lfiack/witns_dsp_som/firmware/grnlr/Core/Inc/main.h

#define __sdram __attribute__((section(".sdram_data")))
#define LED_Pin GPIO_PIN_3
#define LED_GPIO_Port GPIOC
#define VCP_TX_Pin GPIO_PIN_0
#define VCP_TX_GPIO_Port GPIOA
#define VCP_RX_Pin GPIO_PIN_1
#define VCP_RX_GPIO_Port GPIOA
#define ENC_A_Pin GPIO_PIN_2
#define ENC_A_GPIO_Port GPIOA
#define ENC_A_EXTI_IRQn EXTI2_IRQn
#define ENC_B_Pin GPIO_PIN_3
#define ENC_B_GPIO_Port GPIOA
#define OLED_RESET_Pin GPIO_PIN_12
#define OLED_RESET_GPIO_Port GPIOD
#define ENC_PB_Pin GPIO_PIN_13
#define ENC_PB_GPIO_Port GPIOD
#define ENC_PB_EXTI_IRQn EXTI15_10_IRQn
#define SD_DETECT_Pin GPIO_PIN_7
#define SD_DETECT_GPIO_Port GPIOB
