lfiack/witns_dsp_som/firmware/sgtl5000/sgtl5000.h

/*
 * sgtl5000.h
 *
 *  Created on: Oct 14, 2025
 *      Author: laurentf
 */

#ifndef SGTL5000_SGTL5000_H_
#define SGTL5000_SGTL5000_H_

#include "main.h"

typedef enum sgtl5000_registers_enum
{
	SGTL5000_CHIP_ID = 0x0000,
	SGTL5000_CHIP_DIG_POWER = 0x0002,
	SGTL5000_CHIP_CLK_CTRL = 0x0004,
	SGTL5000_CHIP_I2S_CTRL = 0x0006,
	SGTL5000_CHIP_SSS_CTRL = 0x000A,
	SGTL5000_CHIP_ADCDAC_CTRL = 0x000E,
	SGTL5000_CHIP_DAC_VOL = 0x0010,
	SGTL5000_CHIP_PAD_STRENGTH = 0x0014,
	SGTL5000_CHIP_ANA_ADC_CTRL = 0x0020,
	SGTL5000_CHIP_ANA_HP_CTRL = 0x0022,
	SGTL5000_CHIP_ANA_CTRL = 0x0024,
	SGTL5000_CHIP_LINREG_CTRL = 0x0026,
	SGTL5000_CHIP_REF_CTRL = 0x0028,
	SGTL5000_CHIP_MIC_CTRL = 0x002A,
	SGTL5000_CHIP_LINE_OUT_CTRL = 0x002C,
	SGTL5000_CHIP_LINE_OUT_VOL = 0x002E,
	SGTL5000_CHIP_ANA_POWER = 0x0030,
	SGTL5000_CHIP_PLL_CTRL = 0x0032,
	SGTL5000_CHIP_CLK_TOP_CTRL = 0x0034,
	SGTL5000_SHIP_ANA_STATUS = 0x0036,
	SGTL5000_CHIP_ANA_TEST1 = 0x0038,
	SGTL5000_CHIP_ANA_TEST2 = 0x003A,
	SGTL5000_CHIP_SHORT_CTRL = 0x003C,
	SGTL5000_DAP_CONTROL = 0x0100,
	SGTL5000_DAP_PEQ = 0x0102,
	SGTL5000_DAP_BASS_ENHANCE = 0x0104,
	SGTL5000_DAP_BASS_ENHANCE_CTRL = 0x0106,
	SGTL5000_DAP_AUDIO_EQ = 0x0108,
	SGTL5000_DAP_SGTL_SURROUND = 0x010A,
	SGTL5000_DAP_FILTER_COEF_ACCESS = 0x010C,
	SGTL5000_DAP_COEF_WR_B0_MSB = 0x010E,
	SGTL5000_DAP_COEF_WR_B0_LSB = 0x0110,
	SGTL5000_DAP_AUDIO_EQ_BASS_BAND0 = 0x0116,
	SGTL5000_DAP_AUDIO_EQ_BAND1 = 0x0118,
	SGTL5000_DAP_AUDIO_EQ_BAND2 = 0x011A,
	SGTL5000_DAP_AUDIO_EQ_BAND3 = 0x011C,
	SGTL5000_DAP_AUDIO_EQ_TREBLE_BAND4 = 0x011E,
	SGTL5000_DAP_MAIN_CHAN = 0x0120,
	SGTL5000_DAP_MIX_CHAN = 0x0122,
	SGTL5000_DAP_AVC_CTRL = 0x0124,
	SGTL5000_DAP_AVC_THRESHOLD = 0x0126,
	SGTL5000_DAP_AVC_ATTACK = 0x0128,
	SGTL5000_DAP_AVC_DECAY = 0x012A,
	SGTL5000_DAP_COEF_WR_B1_MSB = 0x012C,
	SGTL5000_DAP_COEF_WR_B1_LSB = 0x012E,
	SGTL5000_DAP_COEF_WR_B2_MSB = 0x0130,
	SGTL5000_DAP_COEF_WR_B2_LSB = 0x0132,
	SGTL5000_DAP_COEF_WR_A1_MSB = 0x0134,
	SGTL5000_DAP_COEF_WR_A1_LSB = 0x0136,
	SGTL5000_DAP_COEF_WR_A2_MSB = 0x0138,
	SGTL5000_DAP_COEF_WR_A2_LSB = 0x013A
} sgtl5000_registers_t;

#define SGTL5000_TX_BUFFER_LENGTH (2*100)	// left + right

typedef struct h_sgtl5000_struct
{
	I2C_HandleTypeDef * hi2c;
	SAI_HandleTypeDef * hsai_tx;
	SAI_HandleTypeDef * hsai_rx;

	uint16_t i2c_address;

	uint16_t tx_buffer[SGTL5000_TX_BUFFER_LENGTH];
} h_sgtl5000_t;

HAL_StatusTypeDef sgtl5000_i2c_read_register(h_sgtl5000_t * h_sgtl5000, sgtl5000_registers_t reg_address, uint16_t * data);
HAL_StatusTypeDef sgtl5000_i2c_write_register(h_sgtl5000_t * h_sgtl5000, sgtl5000_registers_t reg_address, uint16_t data);
HAL_StatusTypeDef sgtl5000_i2c_set_bit(h_sgtl5000_t * h_sgtl5000, sgtl5000_registers_t reg_address, uint16_t mask);
HAL_StatusTypeDef sgtl5000_i2c_clear_bit(h_sgtl5000_t * h_sgtl5000, sgtl5000_registers_t reg_address, uint16_t mask);
HAL_StatusTypeDef sgtl5000_init(h_sgtl5000_t * h_sgtl5000);
HAL_StatusTypeDef sgtl5000_enable(h_sgtl5000_t * h_sgtl5000);
HAL_StatusTypeDef sgtl5000_line_in_level(h_sgtl5000_t * h_sgtl5000, uint8_t left, uint8_t right);
HAL_StatusTypeDef sgtl5000_line_out_level(h_sgtl5000_t * h_sgtl5000, uint8_t left, uint8_t right);
HAL_StatusTypeDef sgtl5000_unmute(h_sgtl5000_t * h_sgtl5000);
HAL_StatusTypeDef sgtl5000_i2s_start(h_sgtl5000_t * h_sgtl5000);

#endif /* SGTL5000_SGTL5000_H_ */
