lfiack/witns_dsp_som/firmware/grnlr/grnlr/app.h

#ifndef __APP_H
#define __APP_H

#include "main.h"

#include "coder.h"
#include "sgtl5000.h"
#include "stats.h"
#include "playback.h"

extern h_coder_t h_coder;
extern h_sgtl5000_t h_sgtl5000;
extern h_stats_t h_stats;
extern h_playback_t h_playback;

uint8_t app_init(void);
void app_process(void);
void app_process_audio(int16_t * in_buffer, int16_t * out_buffer, uint16_t len);

#endif // __APP_H
